virpo/pegboard/models/pieces/01_straight_2_holes.stl

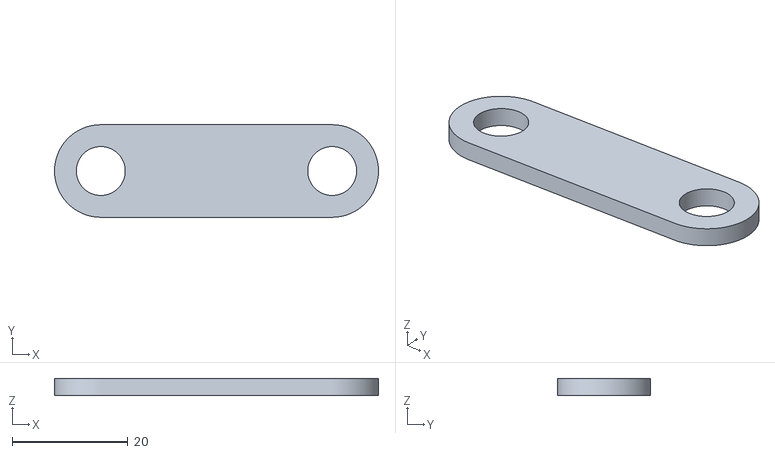
[picture p18: CAD file, 2026-03-30]
models/pieces/01_straight_2_holes.stl
56.0 x 16.0 x 3.00
