virpo/pegboard/models/pieces/all_shapes_layout.stl

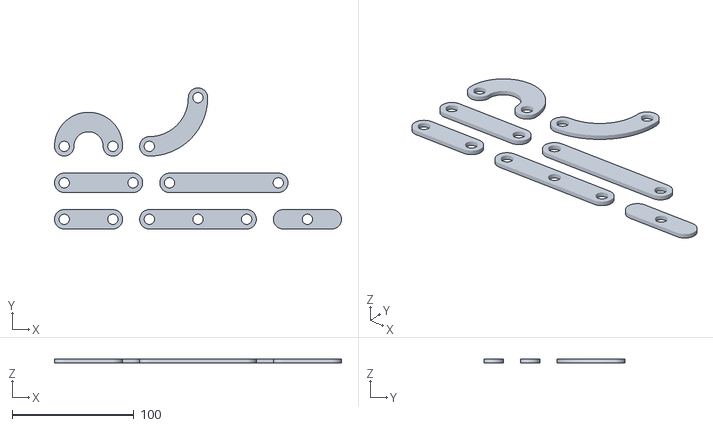
[picture p19: CAD file, 2026-03-30]
models/pieces/all_shapes_layout.stl
236.0 x 116.0 x 3.00
