virpo/pegboard/models/pieces/07_quarter_circle_2_holes.stl

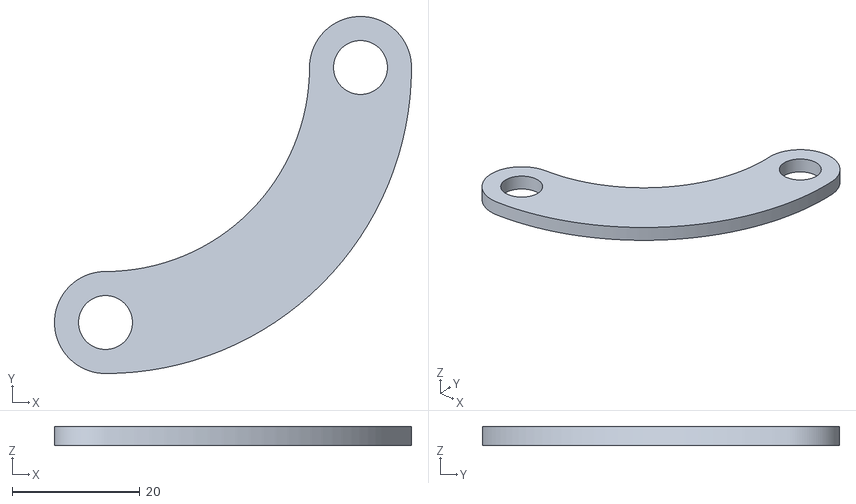
[picture p20: CAD file, 2026-03-30]
models/pieces/07_quarter_circle_2_holes.stl
56.0 x 56.0 x 3.00
